ssjowowo/bleep/design/brand/wordmark.png

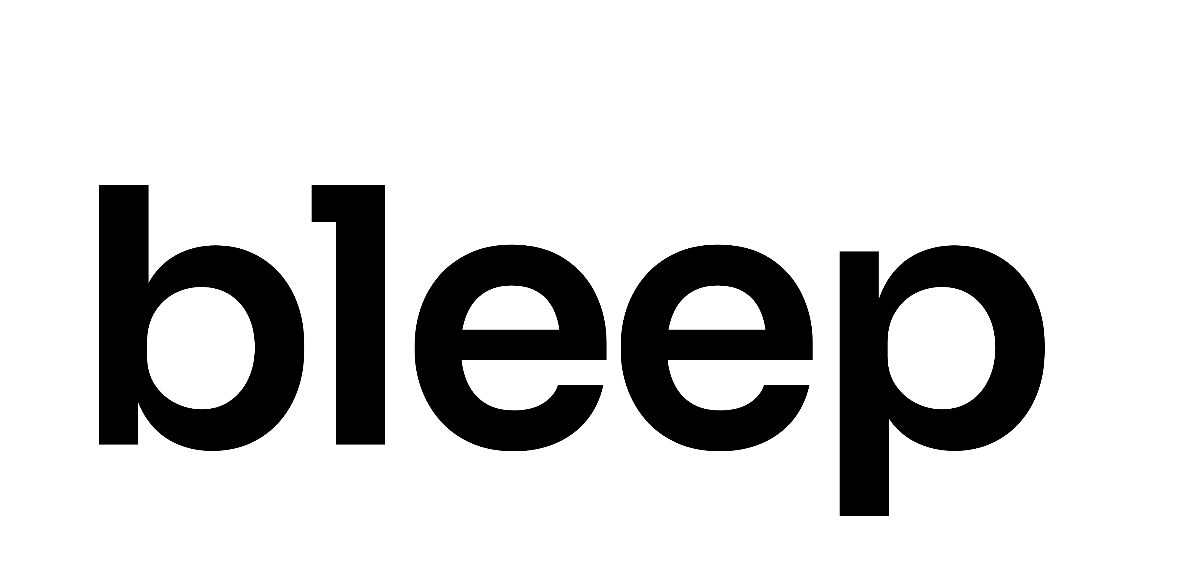
design/brand/wordmark.png
