ssjowowo/bleep/hardware/concepts/antenna-options.png

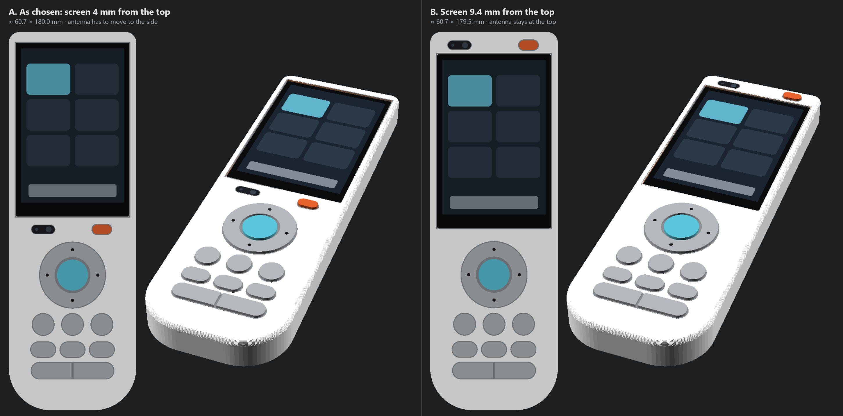
hardware/concepts/antenna-options.png
