ssjowowo/bleep/hardware/concepts/arc_3d0.png

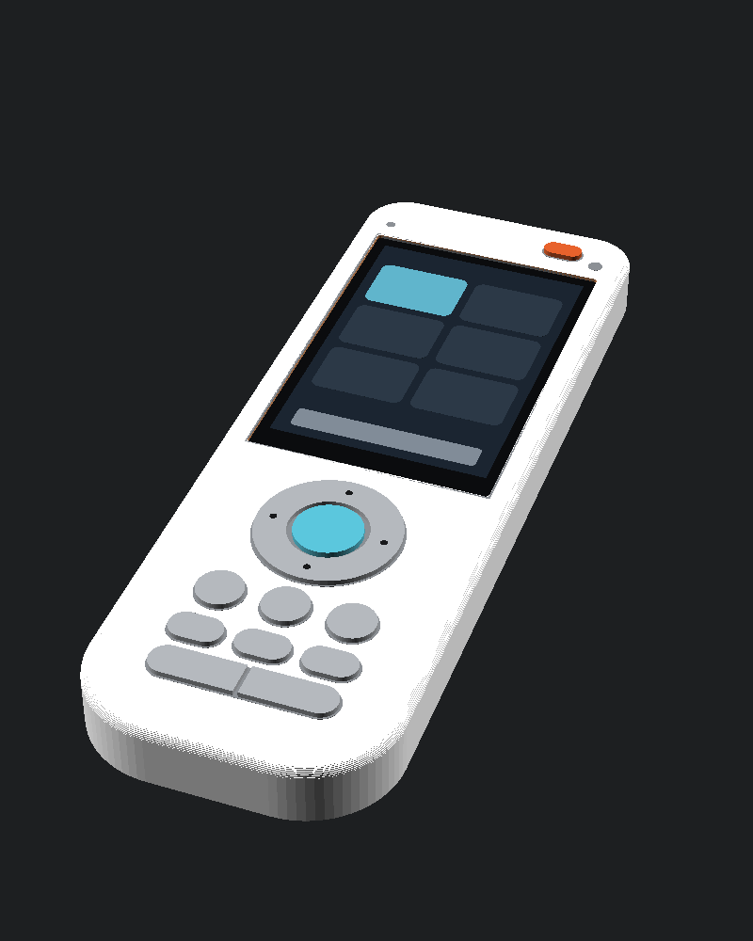
hardware/concepts/arc_3d0.png
