ssjowowo/bleep/hardware/concepts/arc_top0.png

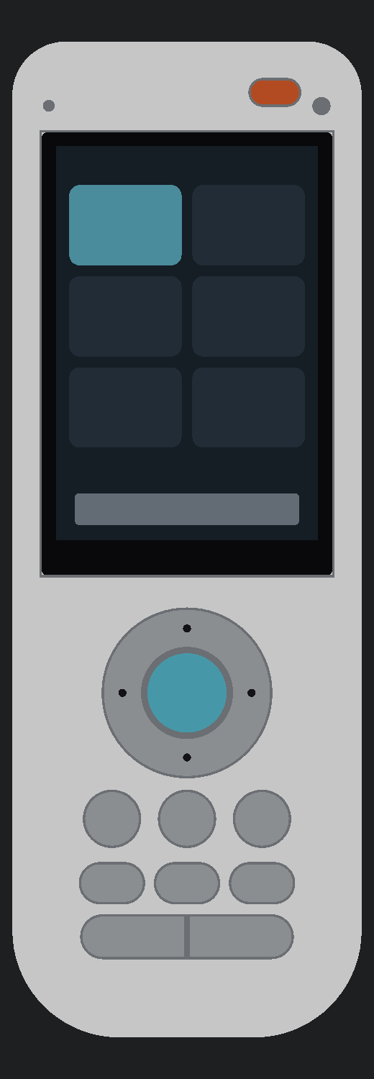
hardware/concepts/arc_top0.png
