ssjowowo/bleep/hardware/concepts/arc_top4.png

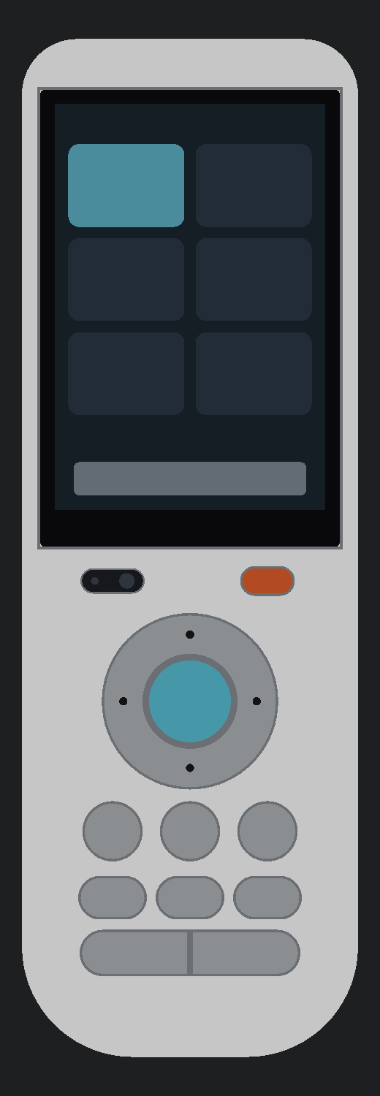
hardware/concepts/arc_top4.png
