ssjowowo/bleep/hardware/concepts/arc_top6.png

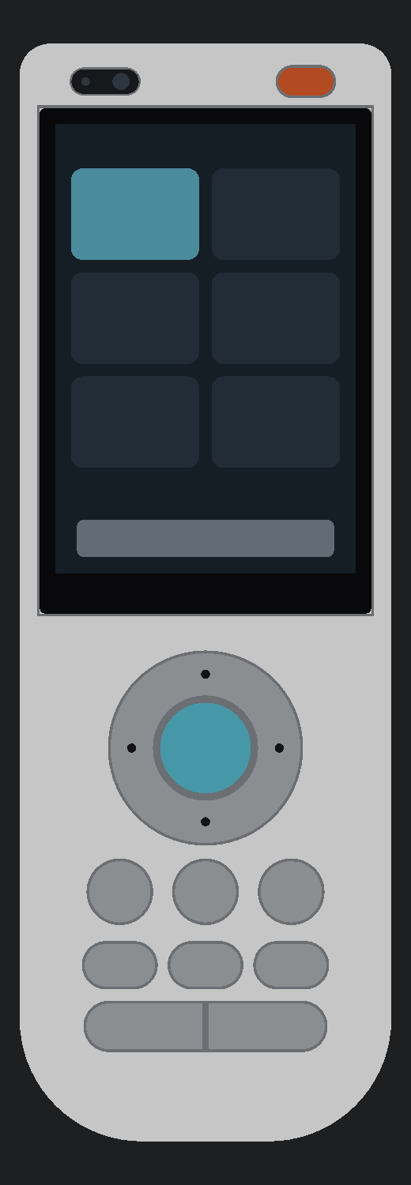
hardware/concepts/arc_top6.png
