ssjowowo/bleep/hardware/concepts/arctic-studies.png

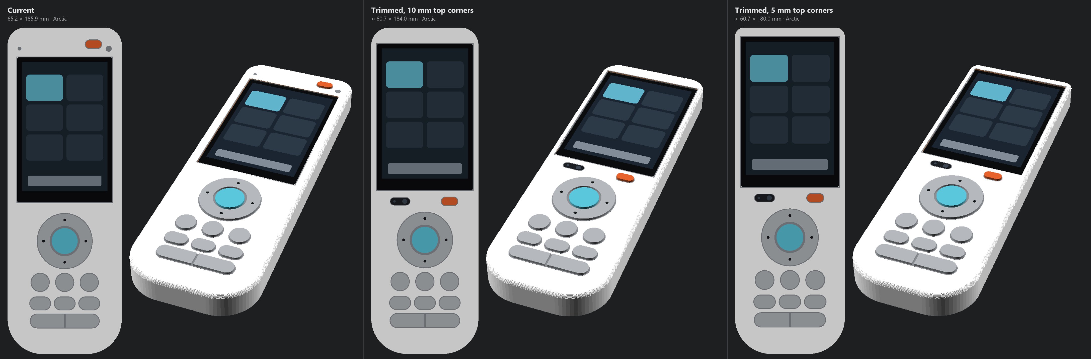
hardware/concepts/arctic-studies.png
