ssjowowo/bleep/hardware/concepts/check.png

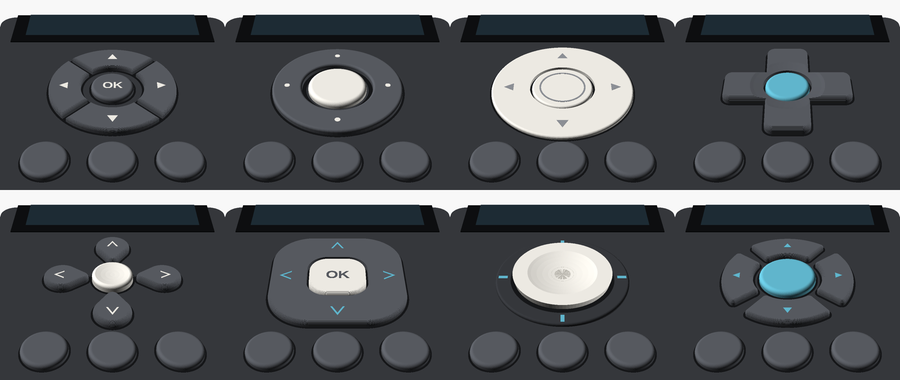
hardware/concepts/check.png
