ssjowowo/bleep/hardware/concepts/chk_3d.png

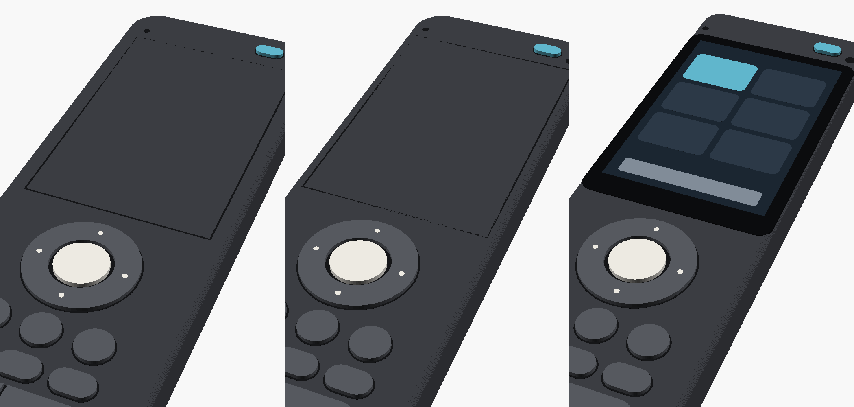
hardware/concepts/chk_3d.png
