ssjowowo/bleep/hardware/concepts/chk_top.png

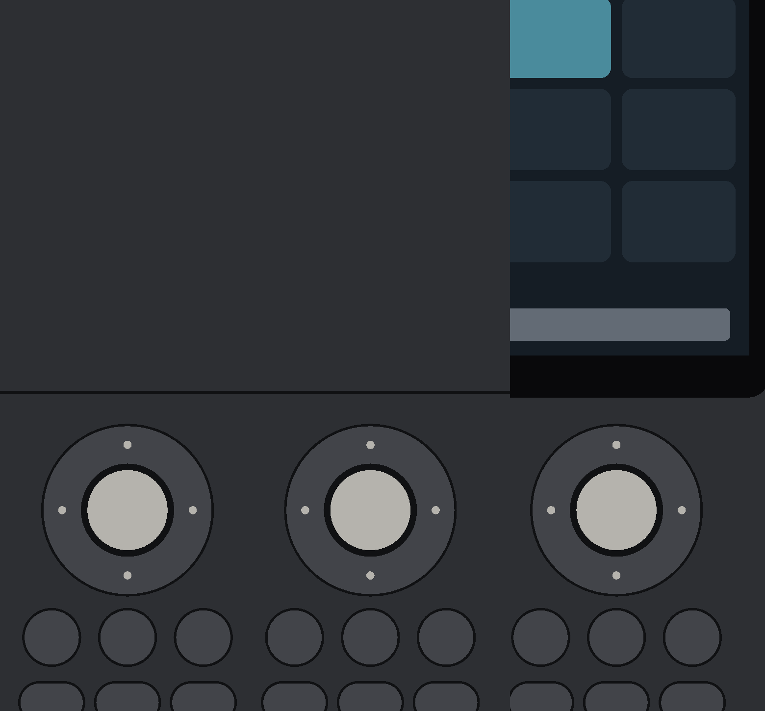
hardware/concepts/chk_top.png
