ssjowowo/bleep/hardware/concepts/dpad-concepts-top.png

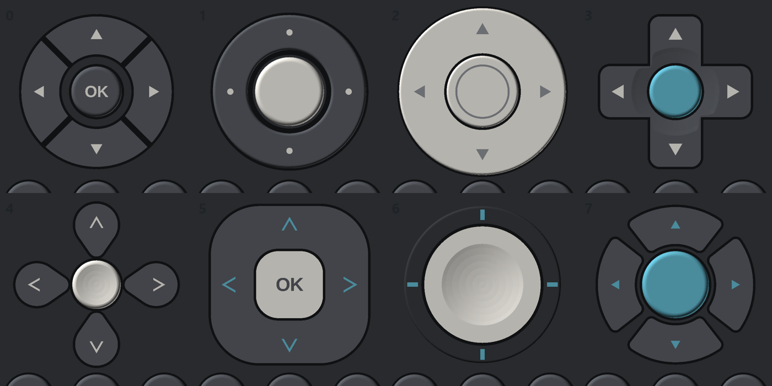
hardware/concepts/dpad-concepts-top.png
