ssjowowo/bleep/hardware/concepts/dpad-concepts.png

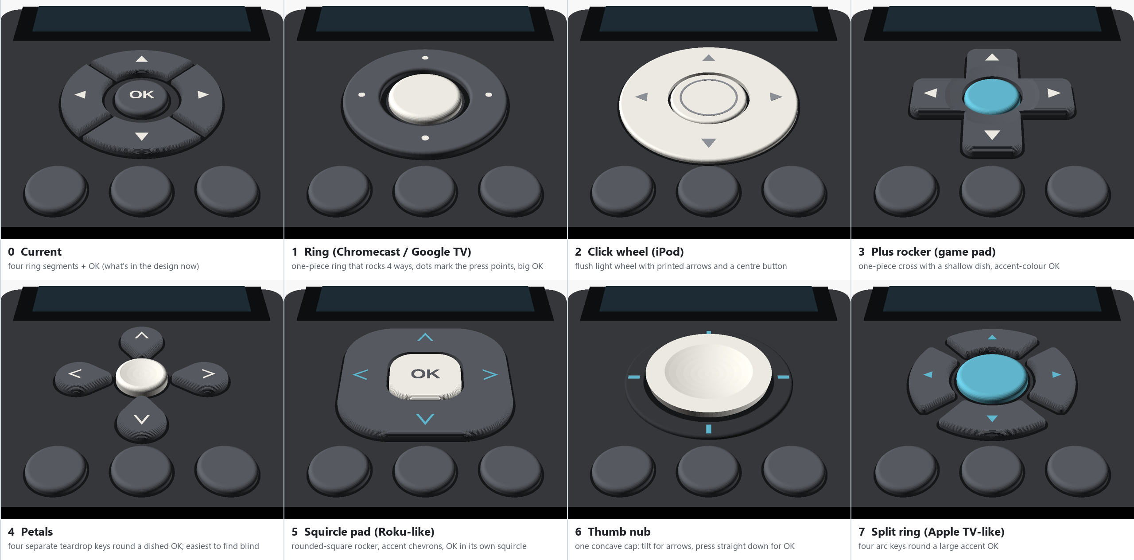
hardware/concepts/dpad-concepts.png
