ssjowowo/bleep/hardware/concepts/slim-fullscreen.png

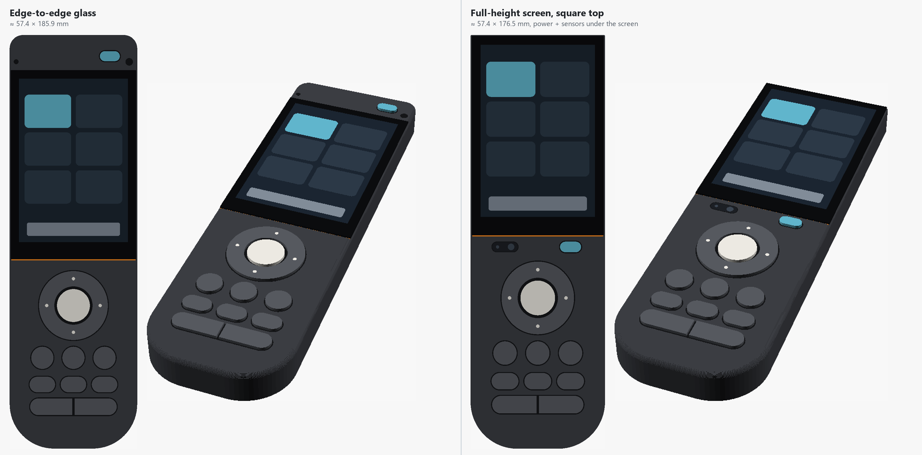
hardware/concepts/slim-fullscreen.png
