ssjowowo/bleep/hardware/concepts/slim-studies.png

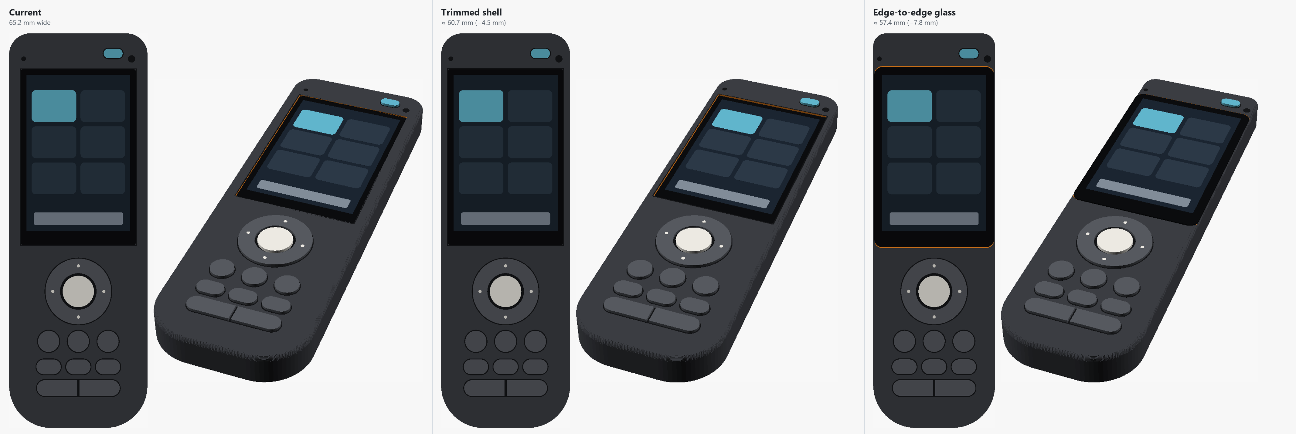
hardware/concepts/slim-studies.png
