ssjowowo/bleep/hardware/concepts/slim-trimmed-r5.png

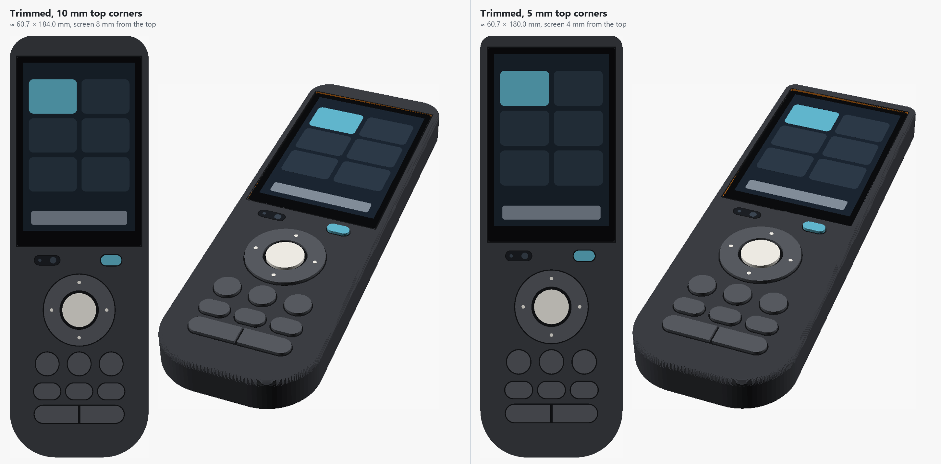
hardware/concepts/slim-trimmed-r5.png
