ssjowowo/bleep/hardware/concepts/slim-trimmed-row.png

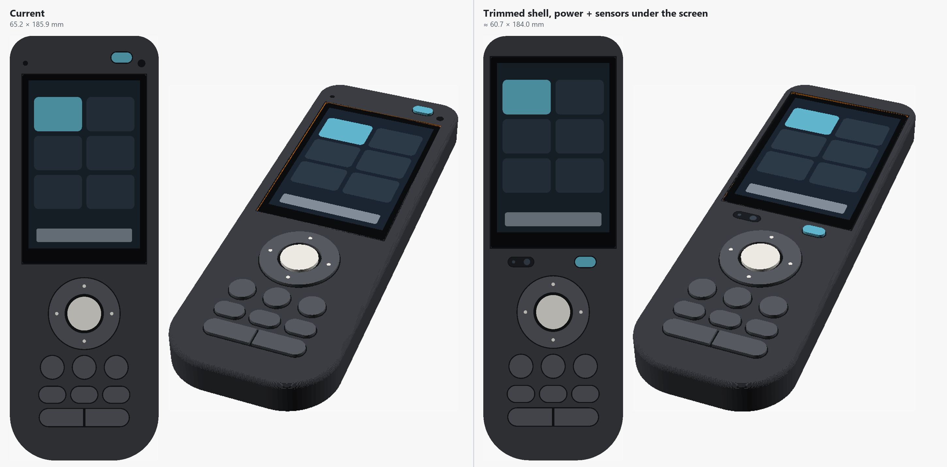
hardware/concepts/slim-trimmed-row.png
