ssjowowo/bleep/hardware/concepts/slim_3d0.png

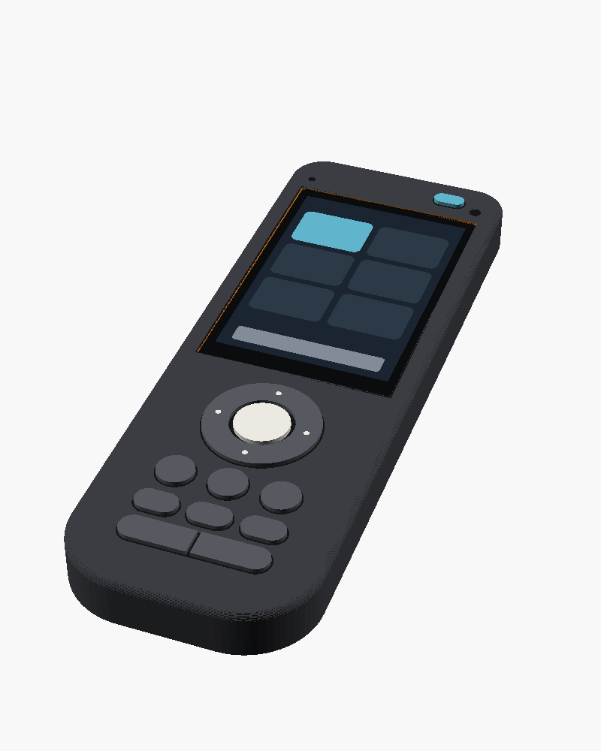
hardware/concepts/slim_3d0.png
