ssjowowo/bleep/hardware/concepts/slim_top0.png

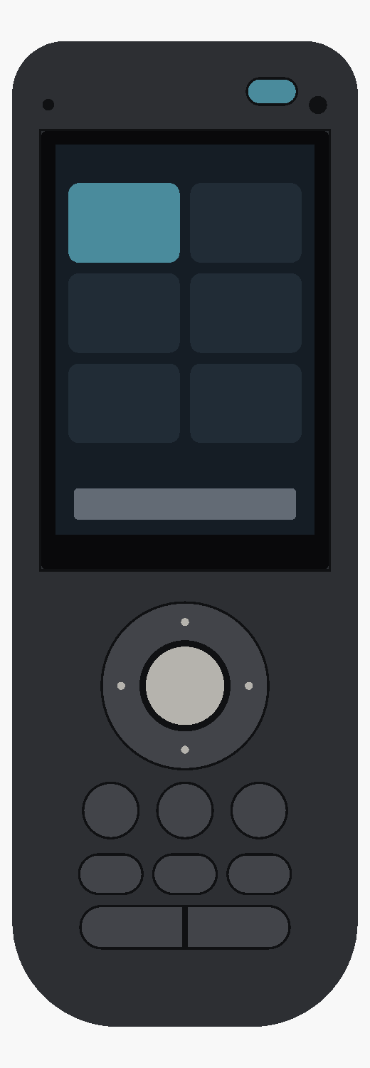
hardware/concepts/slim_top0.png
