ssjowowo/bleep/hardware/concepts/slim_top4.png

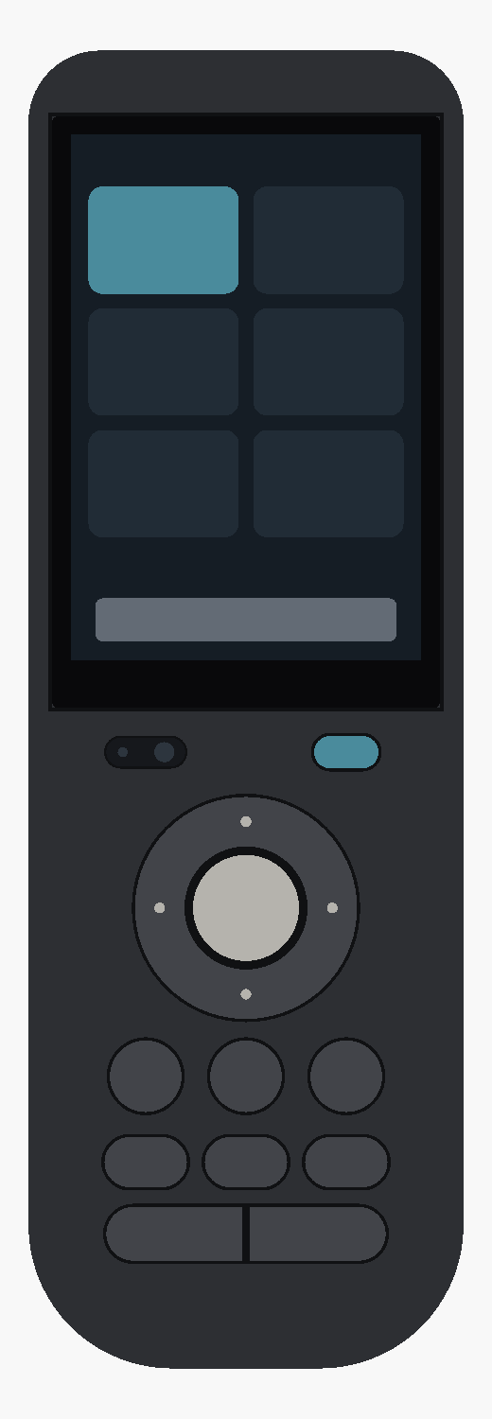
hardware/concepts/slim_top4.png
