ssjowowo/bleep/hardware/concepts/t0.png

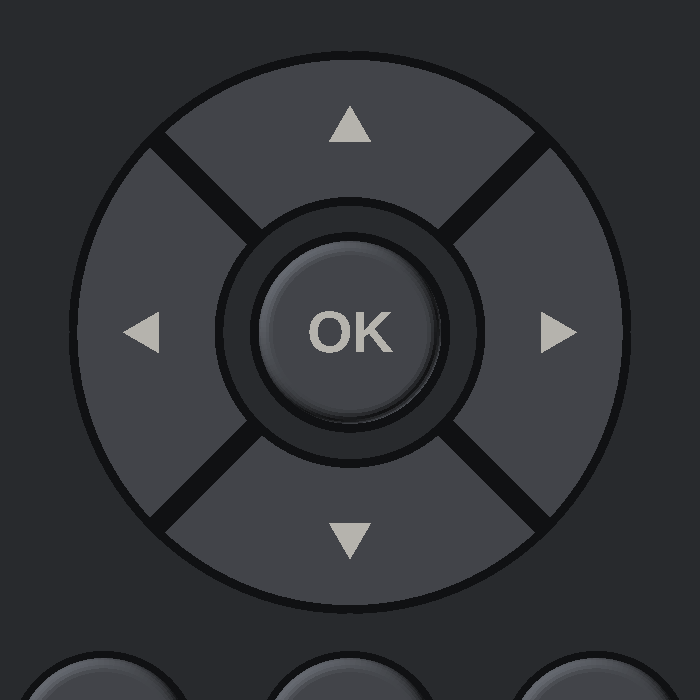
hardware/concepts/t0.png
