ssjowowo/bleep/hardware/concepts/t1.png

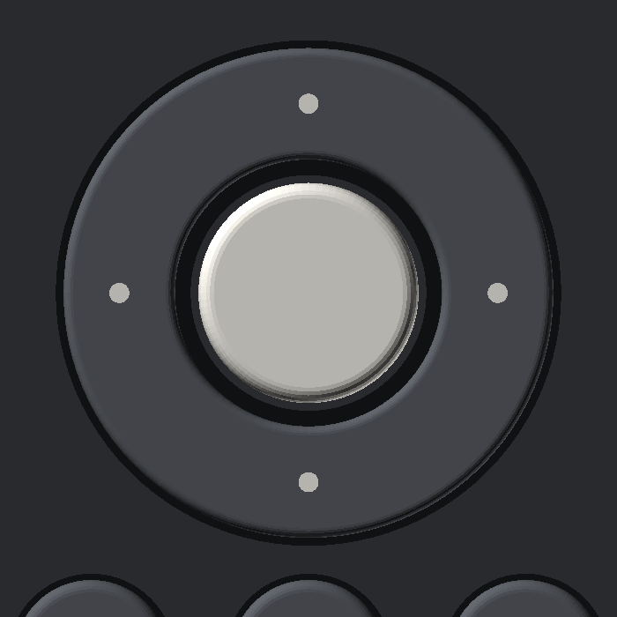
hardware/concepts/t1.png
