ssjowowo/bleep/hardware/concepts/t2.png

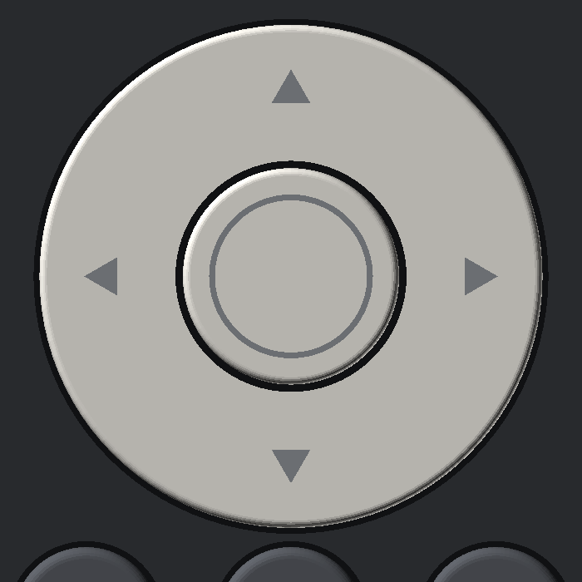
hardware/concepts/t2.png
