ssjowowo/bleep/hardware/concepts/t3.png

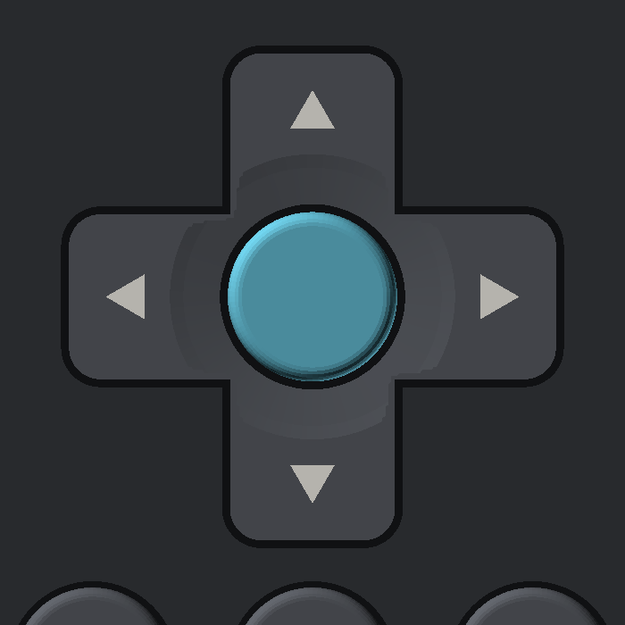
hardware/concepts/t3.png
