ssjowowo/bleep/hardware/concepts/t4.png

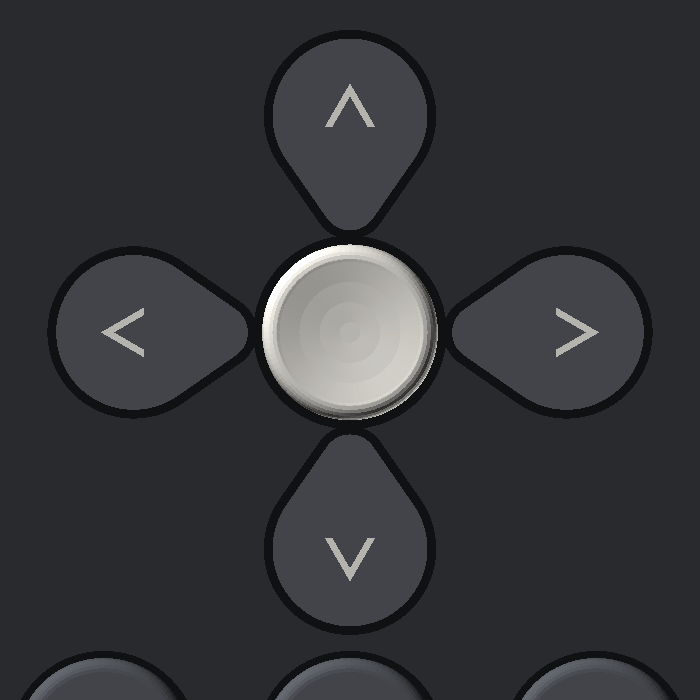
hardware/concepts/t4.png
