ssjowowo/bleep/hardware/concepts/t5.png

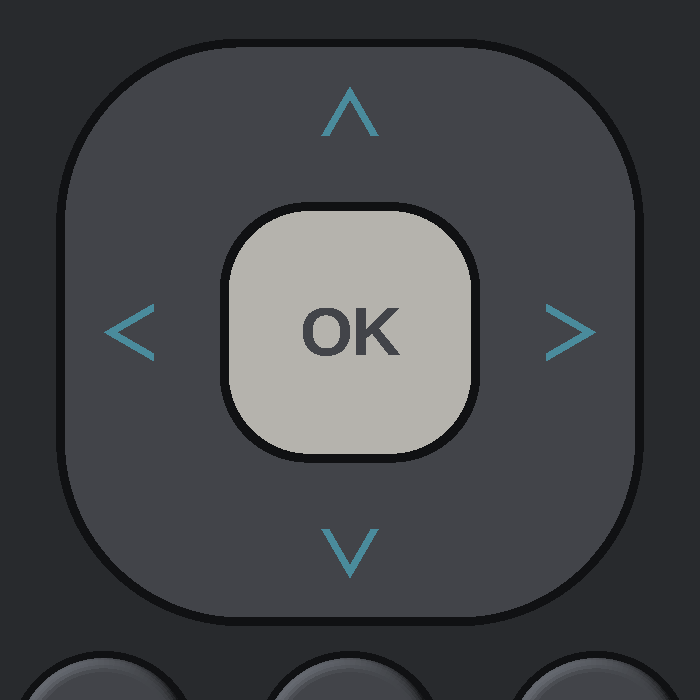
hardware/concepts/t5.png
