ssjowowo/bleep/hardware/concepts/t6.png

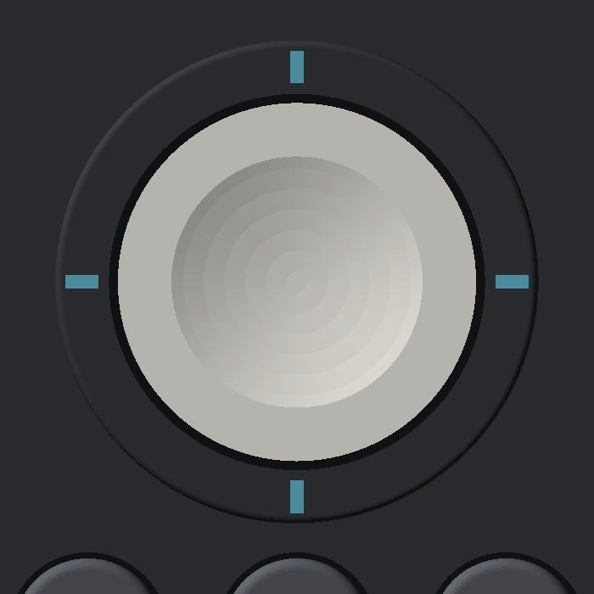
hardware/concepts/t6.png
