ssjowowo/bleep/hardware/concepts/t7.png

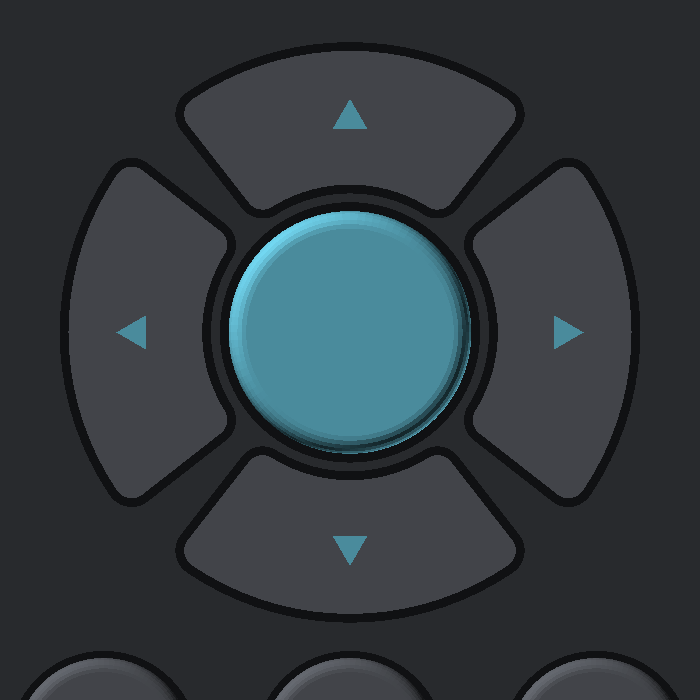
hardware/concepts/t7.png
