ssjowowo/bleep/hardware/concepts/v0.png

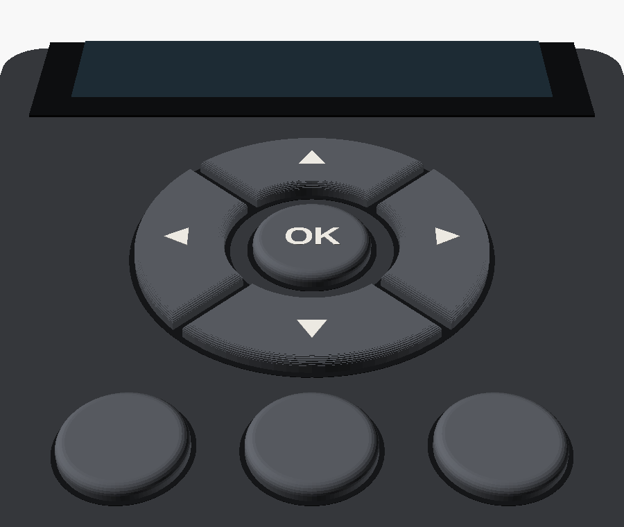
hardware/concepts/v0.png
