ssjowowo/bleep/hardware/concepts/v1.png

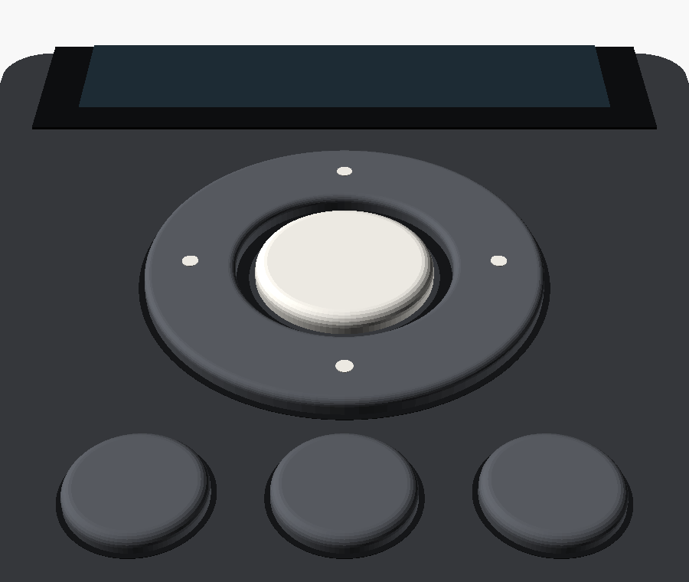
hardware/concepts/v1.png
