ssjowowo/bleep/hardware/concepts/v2.png

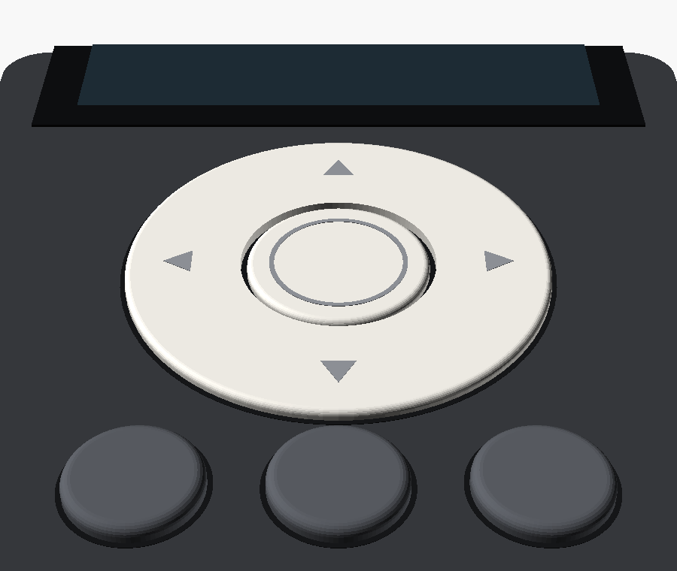
hardware/concepts/v2.png
