ssjowowo/bleep/hardware/concepts/v3.png

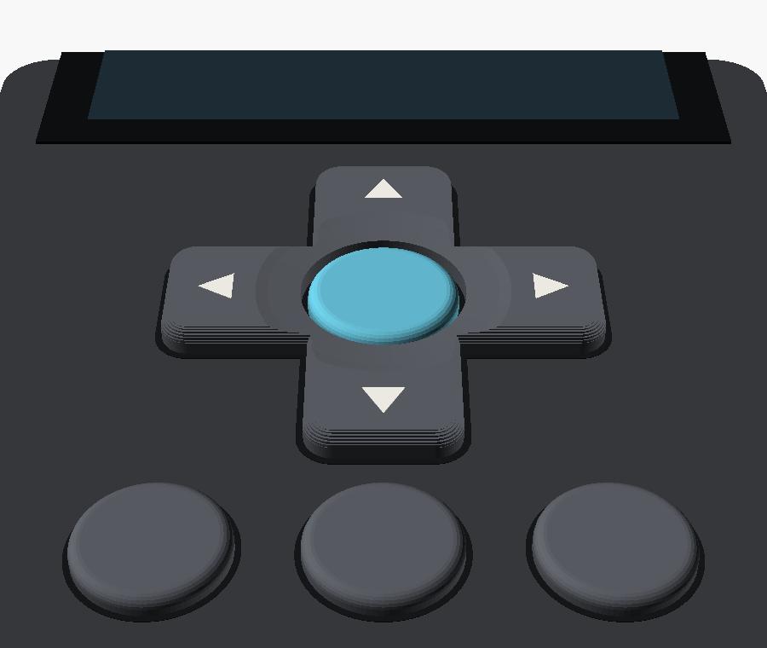
hardware/concepts/v3.png
