ssjowowo/bleep/hardware/concepts/v5.png

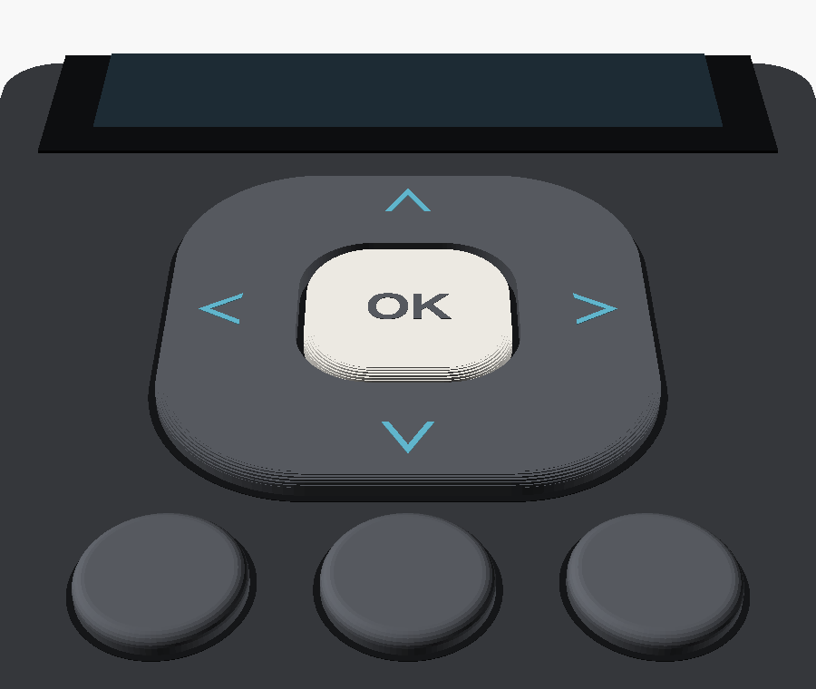
hardware/concepts/v5.png
