ssjowowo/bleep/hardware/concepts/v6.png

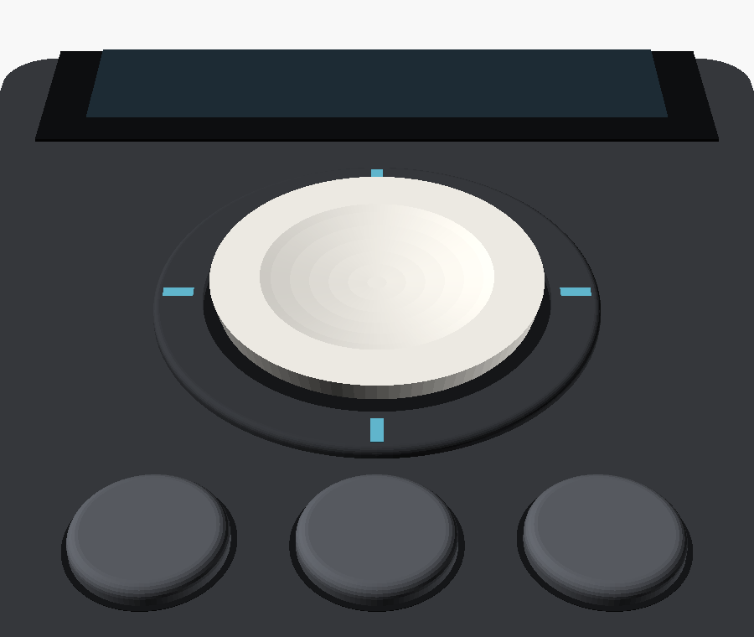
hardware/concepts/v6.png
