ssjowowo/bleep/hardware/docs/enclosure-assembly.png

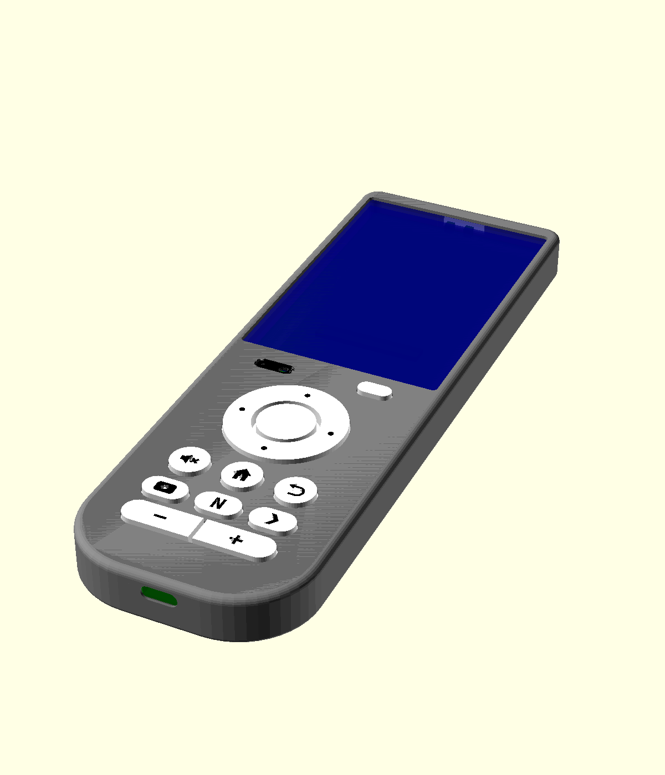
hardware/docs/enclosure-assembly.png
