ssjowowo/bleep/hardware/mainboard/route_debug.png

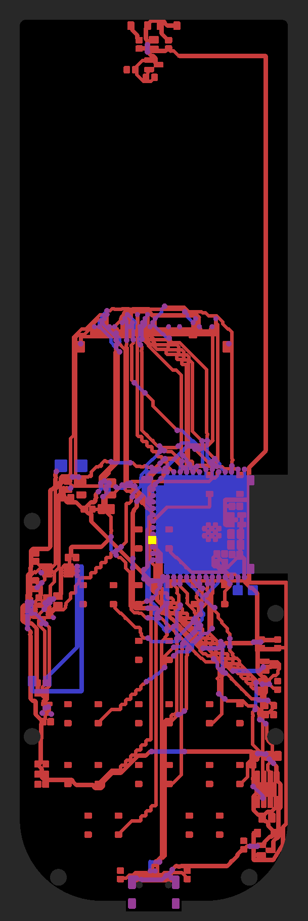
hardware/mainboard/route_debug.png
